MZatar/The-Gater/Images/20260309_160927.jpg

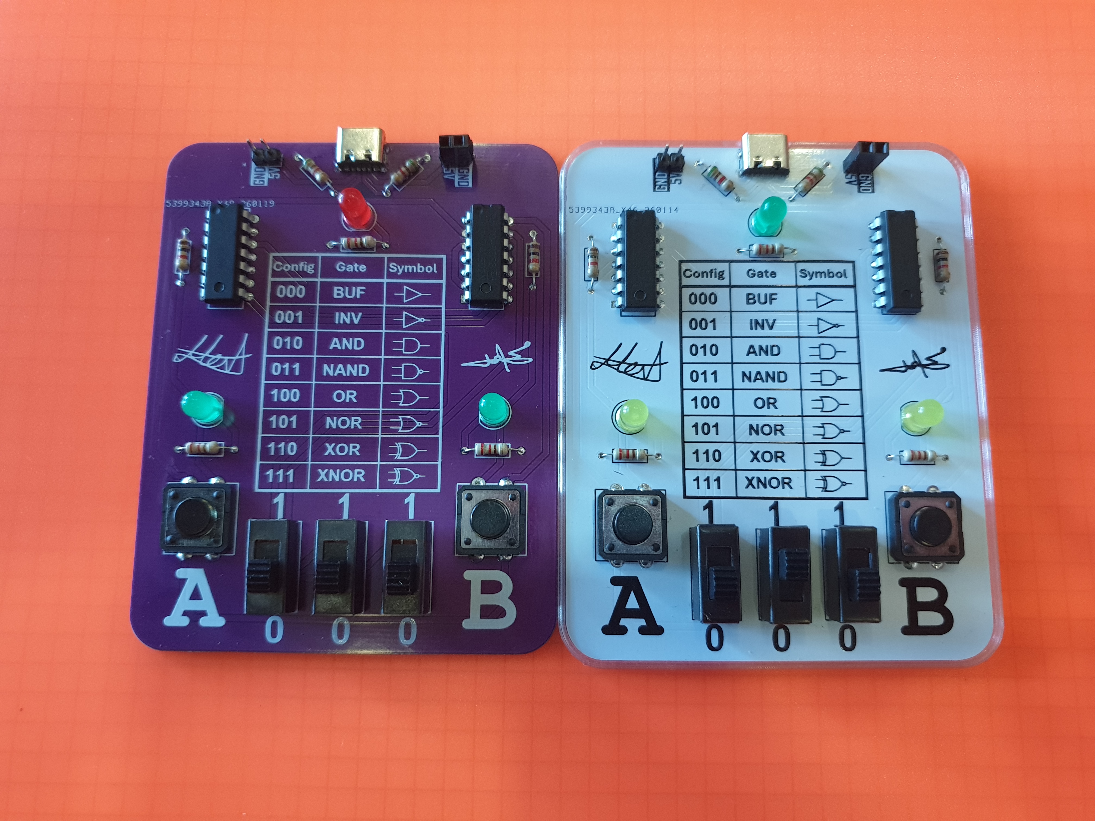
Images/20260309_160927.jpg
