MZatar/The-Gater/Images/20260309_160943.jpg

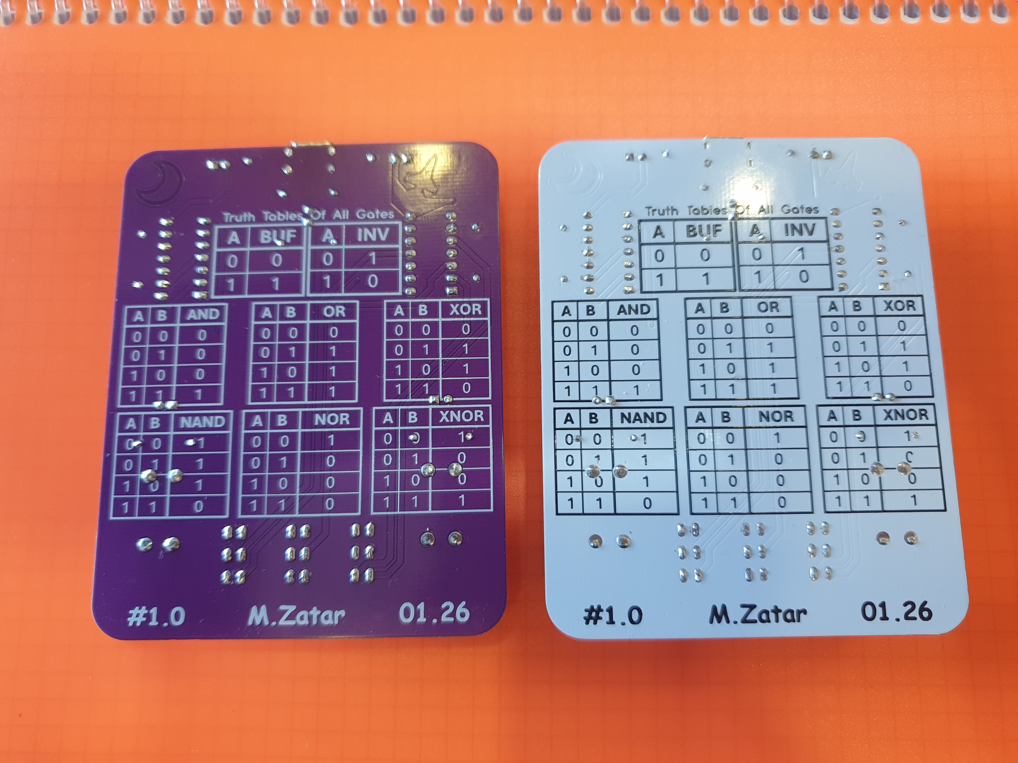
Images/20260309_160943.jpg
